likeablob/miniDenko/images/md_1_sd.gif

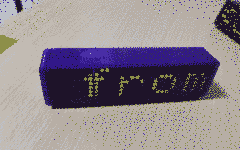
images/md_1_sd.gif
